teapotlaboratories/bwlr1c/docs/images/device_close_up.jpg

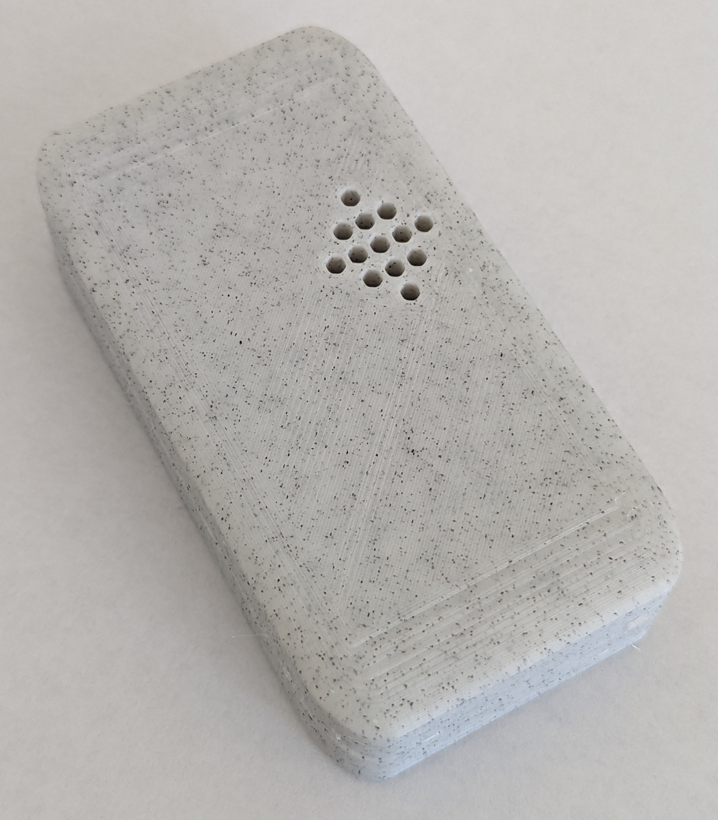
docs/images/device_close_up.jpg
