teapotlaboratories/bwlr1c/docs/images/with_aa_for_comparison.jpg

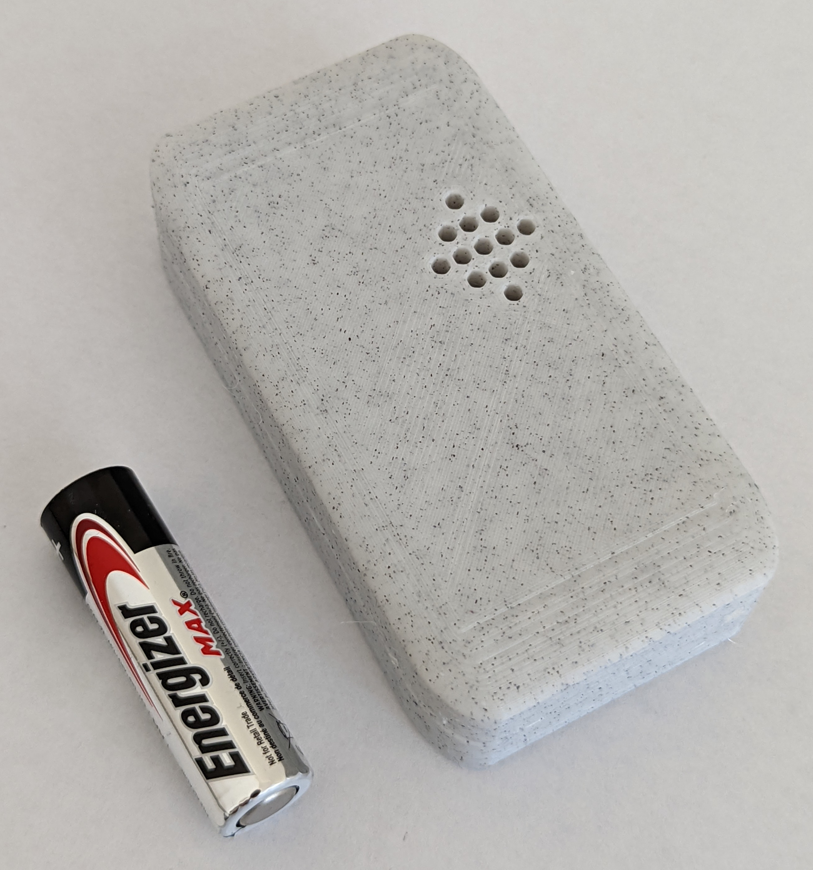
docs/images/with_aa_for_comparison.jpg
